adamforbes92/can2cluster/Images/WiFi3.jpg

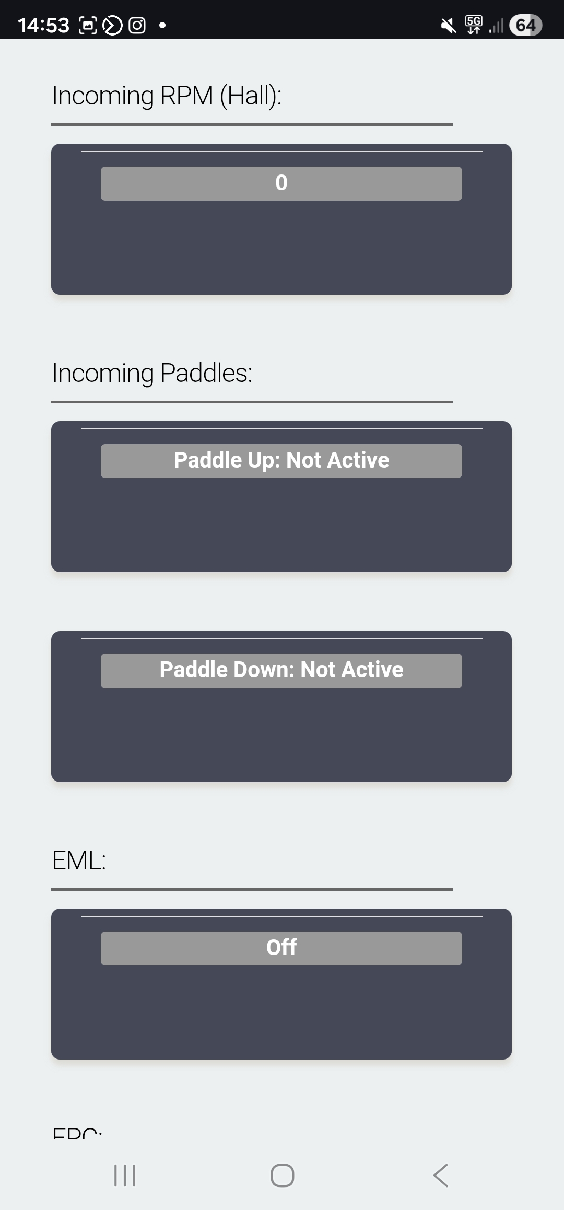
Images/WiFi3.jpg
