adamforbes92/can2cluster/Images/WiFi4.jpg

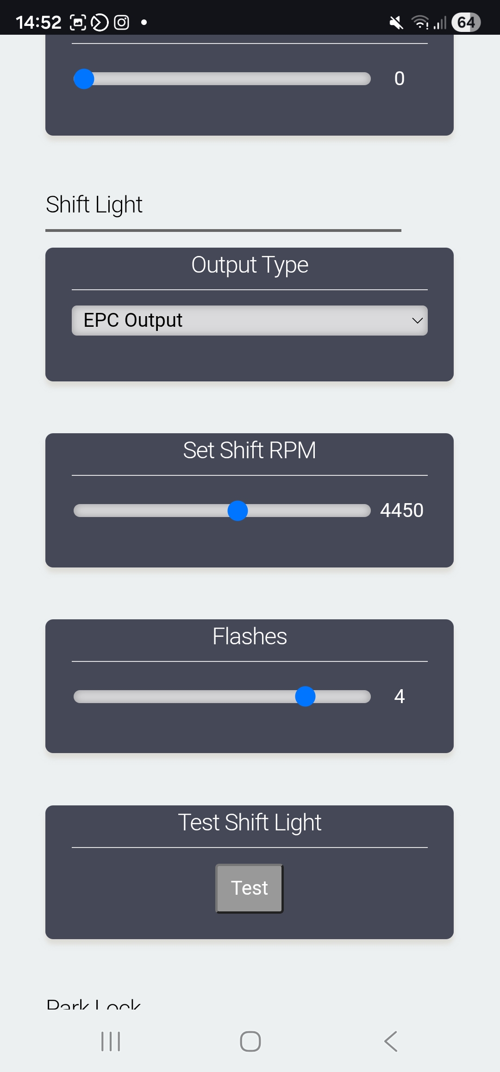
Images/WiFi4.jpg
