adamforbes92/can2cluster/Images/WiFi7.jpg

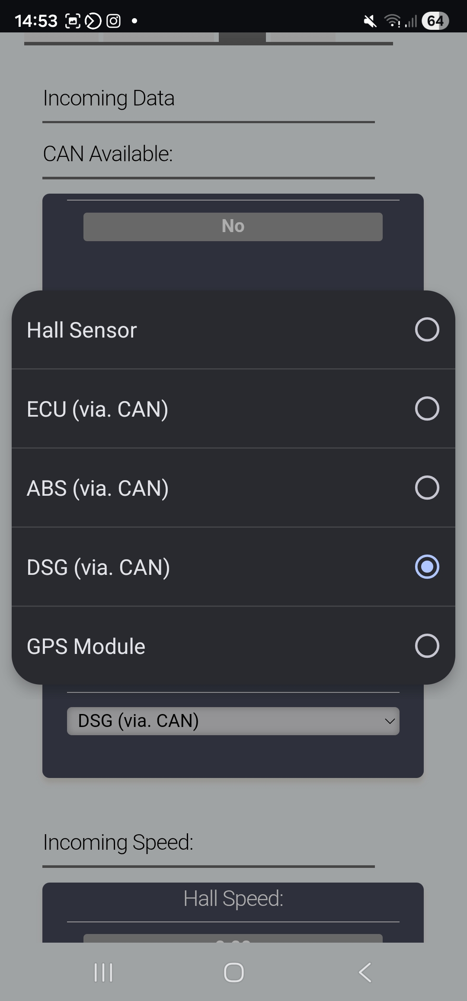
Images/WiFi7.jpg
