adamforbes92/can2cluster/PlatformIO/src/can2cluster_can.cpp

  #include "can2cluster_can.h"
#include "can2cluster_uds.h"
#include "can2cluster_savvycan.h"

void canInit()
{
  // Chassis CAN pins differ between boards (new board reuses GPIO16/26).
  const gpio_num_t txPin = (gpio_num_t)(isNewBoard ? pinTX_CAN_NEW : pinTX_CAN);
  const gpio_num_t rxPin = (gpio_num_t)(isNewBoard ? pinRX_CAN_NEW : pinRX_CAN);

  // Configure TWAI (CAN) controller
  twai_general_config_t g_config = TWAI_GENERAL_CONFIG_DEFAULT(txPin, rxPin, TWAI_MODE_NORMAL);
  g_config.rx_queue_len = 256;
  // Enable alerts so we can detect (and recover from) error-passive / bus-off events.
  g_config.alerts_enabled = TWAI_ALERT_BUS_OFF
                          | TWAI_ALERT_BUS_RECOVERED
                          | TWAI_ALERT_ERR_PASS
                          | TWAI_ALERT_ABOVE_ERR_WARN
                          | TWAI_ALERT_RX_QUEUE_FULL;
  twai_timing_config_t t_config = TWAI_TIMING_CONFIG_500KBITS();
  twai_filter_config_t f_config = TWAI_FILTER_CONFIG_ACCEPT_ALL();

  // Install TWAI driver
  if (twai_driver_install(&g_config, &t_config, &f_config) != ESP_OK)
  {
    DEBUG_CAN("TWAI driver install failed");
    return;
  }

  // Start TWAI driver
  if (twai_start() != ESP_OK)
  {
    DEBUG_CAN("TWAI start failed");
    return;
  }

  // Create a task to handle incoming CAN messages
  xTaskCreate(canReceiveTask, "canReceiveTask", 4096, NULL, 5, NULL);

  // Create a task to watch TWAI alerts and recover from bus-off
  xTaskCreate(canMonitorTask, "canMonitorTask", 3072, NULL, 4, NULL);
}

void canReceiveTask(void *args)
{
  twai_message_t rx_frame;
  while (1)
  {
    while (twai_receive(&rx_frame, 0) == ESP_OK)
    {
      onBodyRX(rx_frame);
      // Forward to SavvyCAN analyzer (no-op when analyzerMode and analyzerSerial are both false)
      analyzerQueueFrame(rx_frame, 0);
      // Route TP2.0 frames to the TP2.0 task queue
      if (tp20RxQueue &&
          (rx_frame.identifier == TP20_DSG_SETUP_RX ||
           rx_frame.identifier == TP20_RX_ID)) {
        xQueueSendToBack(tp20RxQueue, &rx_frame, 0);
      }
      // Route UDS response frames to the UDS task queue
      if (udsRxQueue && rx_frame.identifier == UDS_RX_ID) {
        xQueueSendToBack(udsRxQueue, &rx_frame, 0);
      }
    }
    vTaskDelay(1);
  }
}

// Monitors TWAI alerts and drives bus-off recovery.
//
// Sequence on bus-off:
//   1. TWAI_ALERT_BUS_OFF fires.
//   2. We call twai_initiate_recovery(), which puts the controller into
//      "recovering" state. The controller waits for 128 occurrences of
//      11 consecutive recessive bits before returning to "stopped".
//   3. TWAI_ALERT_BUS_RECOVERED fires when that completes.
//   4. We call twai_start() to bring the driver back online.
void canMonitorTask(void *args)
{
  while (1)
  {
    uint32_t alerts = 0;
    // Block up to 1 s waiting for an alert. read_alerts also clears the bits.
    if (twai_read_alerts(&alerts, pdMS_TO_TICKS(1000)) != ESP_OK)
    {
      continue;
    }

    if (alerts & TWAI_ALERT_ABOVE_ERR_WARN)
    {
      DEBUG_CAN("TWAI: error counter above warning level");
    }
    if (alerts & TWAI_ALERT_ERR_PASS)
    {
      DEBUG_CAN("TWAI: error-passive state entered");
    }
    if (alerts & TWAI_ALERT_RX_QUEUE_FULL)
    {
      DEBUG_CAN("TWAI: RX queue full — frames dropped");
    }
    if (alerts & TWAI_ALERT_BUS_OFF)
    {
      DEBUG_CAN("TWAI: BUS-OFF — initiating recovery");
      hasCAN = false;
      esp_err_t r = twai_initiate_recovery();
      if (r != ESP_OK)
      {
        DEBUG_CAN("TWAI: twai_initiate_recovery() returned %d", (int)r);
      }
    }
    if (alerts & TWAI_ALERT_BUS_RECOVERED)
    {
      DEBUG_CAN("TWAI: bus recovered — restarting driver");
      esp_err_t r = twai_start();
      if (r != ESP_OK)
      {
        DEBUG_CAN("TWAI: twai_start() after recovery returned %d", (int)r);
      }
    }
  }
}

void onBodyRX(const twai_message_t &frame)
{
#if ChassisCANDebug // print incoming CAN messages
  DEBUG_CHASSIS_CAN_("Length: %u ID: 0x%03X Buffer: ", frame.data_length_code, frame.identifier);
  for (uint8_t i = 0; i < frame.data_length_code; i++)
  {
    if (i > 0)
      Serial.print(" ");
    Serial.printf("%02X", frame.data[i]);
  }
  Serial.println();
#endif
  lastCAN = millis();
  hasCAN = true;

  switch (frame.identifier)
  {
  case MOTOR1_ID:
    // frame[2] (byte 3) > motor speed low byte
    // frame[3] (byte 4) > motor speed high byte
    // frame[4] (byte 3) > khm speed?
    vehicleRPMCAN = ((frame.data[3] << 8) | frame.data[2]) * 0.25; // conversion: 0.25*HEX
    break;

  case MOTOR2_ID:
    ecuSpeed = (frame.data[3] * 100 * 128) / 10000;
    break;

  case MOTOR3_ID:
    // Coolant temperature source. TODO(user): confirm the CAN ID, byte index
    // and scaling for your vehicle — this is a placeholder using the VW-style
    // "raw byte 0 minus 40 = degrees C" convention, mirroring how RPM is fixed.
    vehicleCoolantTemp = frame.data[0] - 40;
    break;

  case MOTOR5_ID:
    // set EML & EPC based on the bit read (LSB, so backwards)
    vehicleEML = bitRead(frame.data[1], 5);
    vehicleEPC = bitRead(frame.data[1], 6);
    break;

  case MOTOR6_ID:
    if (frame.data[0] == 0x73 || frame.data[0] == 0x72)
    {
      // vehicleReverse = true;
    }
    else
    {
      // vehicleReverse = false;
    }
    // Note: vehiclePark is authoritatively managed by gearLever_ID (0x448).
    // Only assert park from this frame; never clear it here to avoid racing.
    if (frame.data[0] == 0x83 || frame.data[0] == 0x82)
    {
      vehiclePark = true;
    }
    break;

  case BRAKES3_ID:
    if (1)
    {
      const uint16_t br3_speed_raw = (((uint16_t)frame.data[1] << 8) | frame.data[0]) >> 1;
      absSpeed = (uint16_t)(br3_speed_raw * 0.01f + 0.5f);
    }
    break;

  case mWaehlhebel_1_ID:
    gear_raw = ((frame.data[7] & 0b01110000) >> 4) - 1;
    lever_raw = (frame.data[7] & 0b00000001);

    if (lever_raw)
    {
      gear = gear_raw;
      switch (gear)
      {
      case 3:
        break;
      default:
        break;
      }

      if (gear == 0xFF)
      {
        gear = 1;
      }
    }
    break;

  case gearLever_ID:
    lever = (frame.data[0] & 0b11110000) >> 4;
    switch (lever)
    {
    case LEVER_P:
      vehiclePark = true;
      vehicleReverse = false;
      vehicleNeutral = false;
      break;
    case LEVER_R:
      vehiclePark = false;
      vehicleReverse = true;
      vehicleNeutral = false;
      break;
    case LEVER_N:
      vehiclePark = false;
      vehicleReverse = false;
      vehicleNeutral = true;
      break;
    case LEVER_D:
    case LEVER_S:
    case LEVER_TIPTRONIC_ON:
    case LEVER_TIPTRONIC_UP:
    case LEVER_TIPTRONIC_DOWN:
      vehiclePark = false;
      vehicleReverse = false;
      vehicleNeutral = false;
      break;
    }
    break;

  case emeraldECU1_ID:
    vehicleRPMCAN = ((frame.data[0] << 8) | frame.data[1]);
    break;

  case RENAULT_MEGANE_ECU:
    // Renault Megane engine RPM: bytes 0..1 big-endian, raw/8 (verified against
    // 2K/3K/4K/5K RPM logs — 4000 RPM reads 0x7D00).
    vehicleRPMCAN = (((uint16_t)frame.data[0] << 8) | frame.data[1]) >> 3;
    break;

  case emeraldECU2_ID:
    calcSpeed = ((frame.data[2] << 8) | frame.data[3]) * (2.25 / 256);
    break;

  case fordECU1_ID:
    vehicleRPMCAN = frame.data[1] & 0x00FF;
    vehicleRPMCAN |= (frame.data[0] << 8) & 0x7F00;
    break;

  case fordECU2_ID:
    vehicleOilPressure = (frame.data[5] >> 4) & 0x01;
    vehicleBattLight = (frame.data[4] >> 1) & 0x01;
    vehicleEML = (frame.data[4] >> 6) & 0x03;
    vehicleCoolantTemp = (frame.data[0] & 0xFF) - 40;
    break;

  case MOTOR_12:
  {
    // MQB Motor_12 (0x0A8) - SG_ MO_Drehzahl_01 : 48|16@1+ (0.25,0) [0|16383] "Unit_MinutInver"
    // i.e. engine speed (Drehzahl = revs) in RPM, factor 0.25/bit, 16-bit LE, bytes 6+7.
    const uint16_t mo_drehzahl_raw = ((uint16_t)frame.data[7] << 8) | frame.data[6];
    vehicleRPMCAN = (uint16_t)(mo_drehzahl_raw * 0.25f + 0.5f);
    break;
  }

  case MOTOR_07:
  {
    // MQB Motor_07 (0x640) - SG_ MO_Kuehlmitteltemp : 24|8@1+ (0.75,-48) "degC"  -> byte 3, coolant temperature
    const int16_t coolant_c = (int16_t)(frame.data[3] * 0.75f - 48.0f + 0.5f);
    vehicleCoolantTemp = (coolant_c > 0) ? (uint8_t)coolant_c : 0;
    break;
  }

  case MOTOR_18:
  {
    // MQB Motor_18 (0x670) - SG_ MO_EPCL : 13|3@1+  -> byte 1 bits 5..7, EPC lamp request (0 = off, >0 = lamp/text variants)
    // MQB has no engine MIL (EML) broadcast on FCAN - the check-engine
    // lamp is driven via the OBD/diagnostic path only, so vehicleEML has no MQB source.
    vehicleEPC = ((frame.data[1] >> 5) & 0x07) != 0;
    break;
  }

  case ESP_19:
  {
    // MQB ESP_19 (0x0B2) - per-wheel ABS speeds broadcast.
    // MQB FCAN K-matrix: four 16-bit LE wheel speeds (HL/HR/VL/VR) with
    // factor 0.0075 km/h per bit each.
    //   HL = Hinten Links  (rear left)   -> bytes 0..1
    //   HR = Hinten Rechts (rear right)  -> bytes 2..3
    //   VL = Vorne  Links  (front left)  -> bytes 4..5
    //   VR = Vorne  Rechts (front right) -> bytes 6..7
    // Average all four for a stable vehicle speed (ABS speed source).
    const uint16_t wheel_speed_hl_raw = (frame.data[1] << 8) | frame.data[0];
    const uint16_t wheel_speed_hr_raw = (frame.data[3] << 8) | frame.data[2];
    const uint16_t wheel_speed_vl_raw = (frame.data[5] << 8) | frame.data[4];
    const uint16_t wheel_speed_vr_raw = (frame.data[7] << 8) | frame.data[6];
    absSpeed = (wheel_speed_hl_raw + wheel_speed_hr_raw + wheel_speed_vl_raw + wheel_speed_vr_raw) * (0.0075 / 4.0);
    break;
  }

  case ESP_21:
  {
    // MQB ESP_21 (0x0FD) - ESP/ASR mode + reference speed.
    // MQB FCAN K-matrix:
    //   SG_ ESP_v_Signal : 16@1+ (0.01,0) "km/h"  -> bytes 4..5 LE, vehicle reference speed
    // Mapped to the ECU speed source so MQB works with either speed selection.
    ecuSpeed = (((uint16_t)frame.data[5] << 8) | frame.data[4]) * 0.01;
    break;
  }

  case GETRIEBE_11:
  {
    // MQB Getriebe_11 (0x0AD) - DSG status broadcast.
    //   SG_ GE_Fahrstufe : 42|4@1+  -> byte 5 bits 2..5, gear-lever position
    // Values: 0=init, 5=P, 6=R, 7=N, 8=D, 9=S, 13=tiptronic.
    //   SG_ GE_Zielgang  -> byte 7 high nibble, target/engaged gear (1..7, 0 = none)
    // Verified against OpenHaldex MQB log "gears all inc tip and sport.csv".
    // Also feeds the PQ 'lever'/'gear' globals so the DSG speed source works on MQB.
    const uint8_t fahrstufe = (frame.data[5] >> 2) & 0x0F;
    const uint8_t zielgang = (frame.data[7] >> 4) & 0x0F;
    switch (fahrstufe)
    {
    case MQB_FAHRSTUFE_P:
      vehiclePark = true;
      vehicleReverse = false;
      vehicleNeutral = false;
      lever = LEVER_P;
      gear = 0;
      break;
    case MQB_FAHRSTUFE_R:
      vehiclePark = false;
      vehicleReverse = true;
      vehicleNeutral = false;
      lever = LEVER_R;
      gear = 0;
      break;
    case MQB_FAHRSTUFE_N:
      vehiclePark = false;
      vehicleReverse = false;
      vehicleNeutral = true;
      lever = LEVER_N;
      gear = 0;
      break;
    case MQB_FAHRSTUFE_D:
    case MQB_FAHRSTUFE_S:
    case MQB_FAHRSTUFE_TIP:
      vehiclePark = false;
      vehicleReverse = false;
      vehicleNeutral = false;
      lever = (fahrstufe == MQB_FAHRSTUFE_D) ? LEVER_D
              : (fahrstufe == MQB_FAHRSTUFE_S) ? LEVER_S
                                               : LEVER_TIPTRONIC_ON;
      gear = (zielgang >= 1 && zielgang <= 6) ? zielgang : 0;
      break;
    default:
      // init / unknown - leave current state untouched
      break;
    }
    break;
  }

  case SHIFTER_PADDLE_ID:
  {
    // A real frame from the factory selector (we never receive our own TX).
    // Its presence switches broadcastGRA() into shadow mode.
    shifterRealSeenMs = millis();

    // Shadow: while a paddle press is being held, re-send this exact frame
    // straight away with only the state nibble swapped. Counter and the
    // handshake answer bytes (D3/D4) are the selector's own, so they stay
    // valid. Nothing is sent while idle. See SHIFTER_PADDLE_ID comment.
    const uint8_t txState = shifterTxState;
    if (txState != 0 && frame.data_length_code >= 4)
    {
      twai_message_t shadow = frame;
      shadow.data[1] = (txState << 4) | (frame.data[1] & 0x0F);
      shadow.data[0] = (~shadow.data[1] & 0xF0) | (frame.data[0] & 0x0F);
      if (twai_transmit(&shadow, pdMS_TO_TICKS(5)) != ESP_OK)
      { // failed, ignore - the next real frame is 10 ms away
      }
    }

#if serialDebugPaddles
    // Debug-only decode of the selector's own tip gate. Not wired into
    // padUpFunc/padDownFunc so it can't feed back into our own emulation.
    const uint8_t stateNibble = (frame.data[1] >> 4) & 0x0F;
    if (stateNibble == SHIFTER_PADDLE_STATE_UP)
    {
      DEBUG_PADDLES("Shifter CAN 0x%03X: paddle UP", SHIFTER_PADDLE_ID);
    }
    else if (stateNibble == SHIFTER_PADDLE_STATE_DOWN)
    {
      DEBUG_PADDLES("Shifter CAN 0x%03X: paddle DOWN", SHIFTER_PADDLE_ID);
    }
#endif
    break;
  }

  case SHIFTER_PADDLE_QUERY_ID:
  {
    // Gearbox -> shifter. Latch the payload so broadcastGRA() can answer the
    // query in its next 0x0AF frames (see SHIFTER_PADDLE_QUERY_ID comment).
    shifterQueryRaw = ((uint32_t)frame.data[0] << 16) | ((uint32_t)frame.data[1] << 8) | frame.data[2];
    shifterQueryMs = millis();

#if serialDebugPaddles
    // The hi-nibble is the paddle state the gearbox has accepted: the one
    // place that proves our 0x0AF frames are being taken seriously.
    static uint8_t lastAck = 0xFF;
    const uint8_t ack = frame.data[0] >> 4;
    if (ack != lastAck)
    {
      lastAck = ack;
      DEBUG_PADDLES("Gearbox CAN 0x%03X: accepted paddle state %s", SHIFTER_PADDLE_QUERY_ID,
                    (ack == 0xA) ? "UP" : (ack == 0xB) ? "DOWN" : (ack == 0xE) ? "idle" : "?");
    }
#endif
    break;
  }

  default:
    // do nothing...
    break;
  }

  // Aftermarket / Custom CAN speed input — parsed independently of the VW switch table
  if (useAftermarket && frame.identifier == (aftermarketSpeedID & 0x7FF)) {
    uint8_t lowIdx  = constrain(aftermarketSpeedLowByte,  0, 7);
    uint8_t highIdx = constrain(aftermarketSpeedHighByte, 0, 7);
    uint16_t rawValue;
    if (aftermarketSpeedLittleEndian) {
      // LSB at lowIdx, MSB at highIdx
      rawValue = (uint16_t)frame.data[lowIdx] | ((uint16_t)frame.data[highIdx] << 8);
    } else {
      // Big-endian: MSB at lowIdx, LSB at highIdx (mirrors broadcastSpeed convention)
      rawValue = (uint16_t)frame.data[highIdx] | ((uint16_t)frame.data[lowIdx] << 8);
    }
    double scaled = (rawValue * aftermarketSpeedScale) + aftermarketSpeedOffset;
    aftermarketSpeed = scaled < 0.0 ? 0.0 : scaled;
  }
}

void sendPaddleUpFrame()
{
  twai_message_t paddlesUp{}; // 0x7C0
  paddlesUp.identifier = GRA_ID;
  paddlesUp.data_length_code = 4;
  paddlesUp.data[0] = 0x0E;     // was 0xB7 chksum = byte 2 XOR byte 3 XOR byte 4
  paddlesUp.data[2] = 0x0C;     // was 0x34
  paddlesUp.data[3] = 0x02;     //
  bitSet(paddlesUp.data[3], 1); // set high (trigger)
  if (twai_transmit(&paddlesUp, pdMS_TO_TICKS(100)) != ESP_OK)
  {
    // failed, ignore
  }
}

void sendPaddleDownFrame()
{
  twai_message_t paddlesDown{}; // 0x7C0
  paddlesDown.identifier = GRA_ID;
  paddlesDown.data_length_code = 4;
  paddlesDown.data[0] = 0x0D; // chksum = byte 2 XOR byte 3 XOR byte
  paddlesDown.data[2] = 0x0C;
  paddlesDown.data[3] = 0x01;
  bitSet(paddlesDown.data[3], 1); // set high (trigger)
  if (twai_transmit(&paddlesDown, pdMS_TO_TICKS(100)) != ESP_OK)
  {
    // failed, ignore
  }
}

void broadcastGRA(void *args)
{
  // 0x01 = down, 0x02 = up, 0x03 = both (MQB_PADDLE_* values). One latch feeds
  // three outputs with their own hold times:
  //   PQ GRA 0x38A      20 ms frame, 80 ms pulse (PQ only knows single up/down)
  //   MQB paddle 0x3DD  100 ms frame, MQB_PADDLE_HOLD_MS
  //   selector 0x0AF    10 ms frame (shadow or standalone), SHIFTER_PADDLE_HOLD_MS
  // paddleOutput (web UI) picks which of them actually go on the bus.
  uint8_t activePaddleCmd = 0x00;
  uint32_t graHoldUntilMs = 0;
  uint32_t mqbHoldUntilMs = 0;
  uint32_t shifterHoldUntilMs = 0;

  // This task runs at the selector's 10 ms frame rate (broadcastGRARefresh);
  // the slower frames are divided down from it.
  uint8_t tick = 0; // 0..9, wraps every 100 ms

  while (1)
  {
#if detailedDebugStack
    stackbroadcastGRA = uxTaskGetStackHighWaterMark(NULL); // for capturing how much memory the task is using
#endif

    // Only stream the paddle frames when DSG is the active speed source.
    // The PQ frame must be broadcast continuously (rolling counter + CRC) for
    // the paddles to work, so it can't be gated on a pending paddle press alone
    // — a one-shot frame would break counter/checksum continuity. When DSG isn't
    // selected, nothing goes on the bus and any stale paddle triggers are cleared.
    if (!useDSG)
    {
      padUpTxPending = false;
      padDownTxPending = false;
      activePaddleCmd = 0x00;
      shifterTxState = 0;
      vTaskDelay(pdMS_TO_TICKS(broadcastGRARefresh));
      continue;
    }

    tick = (tick + 1) % 10;
    const bool tick20 = (tick % 2) == 0;
    const bool tick100 = tick == 0;

    const bool sendPQ = (paddleOutput == "PQ") || (paddleOutput == "All");
    const bool sendMQB = (paddleOutput == "MQB") || (paddleOutput == "All");
    const bool sendShifter = (paddleOutput == "Shifter") || (paddleOutput == "All");

    const uint8_t graPulseMS = 80; // PQ GRA: how long to hold the paddle signal high for (ms)

    // Latch a fresh paddle press into all three hold timers.
    uint8_t newCmd = 0x00;
    if (padUpTxPending && padDownTxPending)
    {
#if serialDebugPaddles
      DEBUG_PADDLES("Paddle up/down triggered together");
#endif
      newCmd = MQB_PADDLE_BOTH;
      padUpTxPending = false;
      padDownTxPending = false;
    }
    else if (padUpTxPending)
    {
#if serialDebugPaddles
      DEBUG_PADDLES("Paddle up");
#endif
      newCmd = MQB_PADDLE_UP;
      padUpTxPending = false;
    }
    else if (padDownTxPending)
    {
#if serialDebugPaddles
      DEBUG_PADDLES("Paddle down");
#endif
      newCmd = MQB_PADDLE_DOWN;
      padDownTxPending = false;
    }
    if (newCmd != 0x00)
    {
      const uint32_t now = millis();
      activePaddleCmd = newCmd;
      graHoldUntilMs = now + graPulseMS;
      mqbHoldUntilMs = now + MQB_PADDLE_HOLD_MS;
      shifterHoldUntilMs = now + SHIFTER_PADDLE_HOLD_MS;
    }

    uint8_t graCmd = 0x00;     // what the PQ GRA frame carries this tick
    uint8_t mqbCmd = 0x00;     // what the MQB 0x3DD frame carries this tick
    uint8_t shifterCmd = 0x00; // what the selector 0x0AF frame carries this tick
    if (activePaddleCmd != 0x00)
    {
      const uint32_t now = millis();
      if ((int32_t)(now - graHoldUntilMs) < 0)
      {
        graCmd = activePaddleCmd;
      }
      if ((int32_t)(now - mqbHoldUntilMs) < 0)
      {
        mqbCmd = activePaddleCmd;
      }
      if ((int32_t)(now - shifterHoldUntilMs) < 0)
      {
        shifterCmd = activePaddleCmd;
      }
      if (graCmd == 0x00 && mqbCmd == 0x00 && shifterCmd == 0x00)
      {
        activePaddleCmd = 0x00;
      }
    }

    // --- PQ GRA frame (emulated, 20 ms): rolling counter + XOR checksum. PQ
    // only recognises a single up/down, so a simultaneous press sends no pulse. ---
    if (sendPQ && tick20)
    {
      twai_message_t broadcastGRA{};
      broadcastGRA.identifier = GRA_ID;
      broadcastGRA.data_length_code = 4;
      broadcastGRA.data[1] = 0x00;        // always zero
      broadcastGRA.data[2] = GRA_counter; // full 8-bit rolling counter (0x00 > 0xFF)
      broadcastGRA.data[3] = (graCmd == MQB_PADDLE_BOTH) ? 0x00 : graCmd;

      GRA_crc = 0;
      for (uint8_t i = 2; i < 5; i++)
      {
        GRA_crc ^= broadcastGRA.data[i]; // xor byte 2, 3, 4
      }
      broadcastGRA.data[0] = GRA_crc;

      if (twai_transmit(&broadcastGRA, pdMS_TO_TICKS(100)) != ESP_OK)
      { // failed, ignore
      }

      GRA_counter++;
    }

    // --- MQB wheel-paddle frame (emulated, 100 ms): static carrier from a
    // customer's MQB capture, last byte is the paddle state. No counter/CRC.
    // See MQB_PADDLE_ID comment. ---
    if (sendMQB && tick100)
    {
      twai_message_t mqbPaddle{};
      mqbPaddle.identifier = MQB_PADDLE_ID;
      mqbPaddle.data_length_code = 8;
      mqbPaddle.data[0] = 0x08;
      mqbPaddle.data[1] = 0x04;
      mqbPaddle.data[2] = 0x20;
      mqbPaddle.data[3] = 0x00;
      mqbPaddle.data[4] = 0xFE;
      mqbPaddle.data[5] = 0x00;
      mqbPaddle.data[6] = 0x0A;
      mqbPaddle.data[7] = mqbCmd;

      if (twai_transmit(&mqbPaddle, pdMS_TO_TICKS(100)) != ESP_OK)
      { // failed, ignore
      }
    }

    // --- Selector paddle frame 0x0AF: real ID/encoding verified directly at
    // the selector module (see SHIFTER_PADDLE_ID comment). ---
    const uint8_t shifterState = (shifterCmd == MQB_PADDLE_UP)     ? SHIFTER_PADDLE_STATE_UP
                                 : (shifterCmd == MQB_PADDLE_DOWN) ? SHIFTER_PADDLE_STATE_DOWN
                                                                   : SHIFTER_PADDLE_STATE_IDLE;

    // Publish the held state for the shadow path in onBodyRX(); 0 keeps it quiet.
    shifterTxState = (!sendShifter || shifterState == SHIFTER_PADDLE_STATE_IDLE) ? 0 : shifterState;

    if (!sendShifter)
    {
      vTaskDelay(pdMS_TO_TICKS(broadcastGRARefresh));
      continue;
    }

    // Shadow mode: the factory selector is on the bus, so it owns 0x0AF.
    // onBodyRX() re-sends its frames with our state during a press; sending
    // our own free-running frame here would only collide with it.
    const uint32_t realSeenMs = shifterRealSeenMs;
    if (realSeenMs != 0 && (millis() - realSeenMs) < SHIFTER_PADDLE_REAL_TIMEOUT_MS)
    {
      vTaskDelay(pdMS_TO_TICKS(broadcastGRARefresh));
      continue;
    }

    // Standalone mode (no selector on the bus): send 0x0AF every 10 ms and
    // answer the gearbox's latest 0x128 query ourselves, exactly as the
    // factory selector does; with no recent query D3/D4 stay 00 00.
    uint8_t answerD3 = 0x00, answerD4 = 0x00;
    const uint32_t queryMs = shifterQueryMs;
    if (queryMs != 0 && (millis() - queryMs) < SHIFTER_PADDLE_QUERY_TIMEOUT_MS)
    {
      const uint32_t q = shifterQueryRaw;
      const uint8_t qD1 = (q >> 16) & 0xFF, qD2 = (q >> 8) & 0xFF, qD3 = q & 0xFF;
      if ((qD1 & 0x0F) == 0x5)
      {
        static const char ident[] = SHIFTER_PADDLE_IDENT;
        answerD4 = 0x01;
        if (qD2 != 0xFF)
        {
          answerD3 = (qD3 == 0xFF) ? (uint8_t)~qD2 : qD2; // complement / echo
        }
        else if (qD3 < sizeof(ident) - 1)
        {
          answerD3 = (uint8_t)ident[qD3]; // part number byte n
        }
        else
        {
          answerD3 = 0x00; // n >= 16 (up to 0x13) answers 0x00 on the real module
        }
      }
    }

    twai_message_t shifterPaddle{};
    shifterPaddle.identifier = SHIFTER_PADDLE_ID;
    shifterPaddle.data_length_code = 4;
    shifterPaddle.data[1] = (shifterState << 4) | (shifterPaddleCounter & 0x0F);
    shifterPaddle.data[0] = (~shifterPaddle.data[1] & 0xF0) | 0x02;
    shifterPaddle.data[2] = answerD3;
    shifterPaddle.data[3] = answerD4;

    if (twai_transmit(&shifterPaddle, pdMS_TO_TICKS(100)) != ESP_OK)
    { // failed, ignore
    }

    shifterPaddleCounter++;

    vTaskDelay(pdMS_TO_TICKS(broadcastGRARefresh));
  }
}

void broadcastSpeed(void *args)
{
  while (1)
  {
#if detailedDebugStack
    stackbroadcastSpeed = uxTaskGetStackHighWaterMark(NULL); // for capturing how much memory the task is using
#endif

    if (!broadcastSpeedEnabled)
    {
      vTaskDelay(pdMS_TO_TICKS(broadcastSpeedRefresh));
      continue;
    }

    twai_message_t speedFrame{};
    speedFrame.identifier = broadcastSpeedID & 0x7FF;
    speedFrame.extd = 0;
    speedFrame.data_length_code = constrain(broadcastSpeedDLC, 0, 8);

    for (uint8_t i = 0; i < 8; i++)
    {
      speedFrame.data[i] = broadcastSpeedData[i];
    }

    int32_t scaledSpeed = static_cast<int32_t>((vehicleSpeed * broadcastSpeedScale) + broadcastSpeedOffset);
    scaledSpeed = constrain(scaledSpeed, 0, 65535);
    broadcastSpeedValue = static_cast<uint16_t>(scaledSpeed);

    uint8_t lowByteIndex = constrain(broadcastSpeedLowByte, 0, 7);
    uint8_t highByteIndex = constrain(broadcastSpeedHighByte, 0, 7);
    uint8_t lowByte = static_cast<uint8_t>(broadcastSpeedValue & 0xFF);
    uint8_t highByte = static_cast<uint8_t>((broadcastSpeedValue >> 8) & 0xFF);

    if (broadcastSpeedLittleEndian)
    {
      speedFrame.data[lowByteIndex] = lowByte;
      speedFrame.data[highByteIndex] = highByte;
    }
    else
    {
      speedFrame.data[lowByteIndex] = highByte;
      speedFrame.data[highByteIndex] = lowByte;
    }

#if serialDebugIO
    DEBUG_IO_("TX SPEED ID:0x%03X DLC:%u Data:", speedFrame.identifier, speedFrame.data_length_code);
    for (uint8_t i = 0; i < speedFrame.data_length_code; i++)
    {
      DEBUG_IO_(" %02X", speedFrame.data[i]);
    }
    DEBUG_IO(" Value:%u (vehicleSpeed:%u)", broadcastSpeedValue, vehicleSpeed);
#endif

    if (twai_transmit(&speedFrame, pdMS_TO_TICKS(5)) != ESP_OK)
    {
      // frame dropped if TX queue is full
    }

    vTaskDelay(pdMS_TO_TICKS(broadcastSpeedRefresh));
  }
}
