adamforbes92/can2cluster/Code/can2cluster_wifi.ino

void setupUI() {
  ESPUI.setVerbosity(Verbosity::Quiet);  // turn off verbose debugging (Verbose for ON; Quiet for OFF)
  ESPUI.sliderContinuous = true;         // update slider valves constantly disabled.  No need and can cause crashes

  // create basic tab
  auto tabBasic = ESPUI.addControl(Tab, "", "Basic");
  ESPUI.addControl(Separator, "Needle Sweep", "", Dark, tabBasic);
  bool_NeedleSweep = ESPUI.addControl(Switcher, "Needle Sweep", String(hasNeedleSweep), Dark, tabBasic, generalCallback);
  int16_sweepSpeed = ESPUI.addControl(Slider, "Rate of Change (ms)", String(sweepSpeed), Dark, tabBasic, generalCallback);
  ESPUI.addControl(Min, "", "0", Dark, int16_sweepSpeed);
  ESPUI.addControl(Max, "", "50", Dark, int16_sweepSpeed);

  int16_stepRPM = ESPUI.addControl(Slider, "Rate RPM", String(stepRPM), Dark, tabBasic, generalCallback);
  ESPUI.addControl(Min, "", "100", Dark, int16_stepRPM);
  ESPUI.addControl(Max, "", "400", Dark, int16_stepRPM);

  int16_stepSpeed = ESPUI.addControl(Slider, "Rate Speed", String(stepSpeed), Dark, tabBasic, generalCallback);
  ESPUI.addControl(Min, "", "100", Dark, int16_stepSpeed);
  ESPUI.addControl(Max, "", "400", Dark, int16_stepSpeed);

  ESPUI.addControl(Button, "Test Needle Sweep", "Test", Dark, tabBasic, extendedCallback, (void *)11);

  // create advanced tab
  auto tabAdvanced = ESPUI.addControl(Tab, "", "Advanced Controls");
  ESPUI.addControl(Separator, "Testing", "", Dark, tabAdvanced);
  bool_testSpeedo = ESPUI.addControl(Switcher, "Test Speedo", "", Dark, tabAdvanced, generalCallback);
  int16_tempSpeed = ESPUI.addControl(Slider, "Go to Speed", String(tempSpeed), Dark, tabAdvanced, generalCallback);
  ESPUI.addControl(Min, "", "0", Dark, int16_tempSpeed);
  ESPUI.addControl(Max, "", "200", Dark, int16_tempSpeed);

  ESPUI.addControl(Separator, "RPM Output", "", Dark, tabAdvanced);
  bool_coilType = ESPUI.addControl(Switcher, "Coil Type", String(coilType), Dark, tabAdvanced, generalCallback);

  bool_testRPM = ESPUI.addControl(Switcher, "Test RPM", "", Dark, tabAdvanced, generalCallback);
  int16_tempRPM = ESPUI.addControl(Slider, "Go to RPM", String(tempRPM), Dark, tabAdvanced, generalCallback);
  ESPUI.addControl(Min, "", "0", Dark, int16_tempRPM);
  ESPUI.addControl(Max, "", "8000", Dark, int16_tempRPM);

  ESPUI.addControl(Separator, "Shift Light", "", Dark, tabAdvanced);
  int16_shiftLight = ESPUI.addControl(Select, "Output Type", "", Dark, tabAdvanced, generalCallback);
  ESPUI.addControl(Option, "None", "None", Dark, int16_shiftLight);
  ESPUI.addControl(Option, "EML Output", "EML", Dark, int16_shiftLight);
  ESPUI.addControl(Option, "EPC Output", "EPC", Dark, int16_shiftLight);
  ESPUI.addControl(Option, "EML & EPC Output", "Both", Dark, int16_shiftLight);

  int16_shiftRPM = ESPUI.addControl(Slider, "Set Shift RPM", String(shiftLimit), Dark, tabAdvanced, generalCallback);
  ESPUI.addControl(Min, "", "0", Dark, int16_shiftRPM);
  ESPUI.addControl(Max, "", "8000", Dark, int16_shiftRPM);

  int16_shiftFlashes = ESPUI.addControl(Slider, "Flashes", String(shiftFlashes), Dark, tabAdvanced, generalCallback);
  ESPUI.addControl(Min, "", "0", Dark, int16_shiftFlashes);
  ESPUI.addControl(Max, "", "5", Dark, int16_shiftFlashes);
  ESPUI.addControl(Button, "Test Shift Light", "Test", Dark, tabAdvanced, extendedCallback, (void *)12);

  ESPUI.addControl(Separator, "RPM Limits:", "", Dark, tabAdvanced);
  int16_maxRPM = ESPUI.addControl(Slider, "Maximum RPM", String(maxRPM), Dark, tabAdvanced, generalCallback);
  ESPUI.addControl(Min, "", "0", Dark, int16_minRPM);
  ESPUI.addControl(Max, "", "400", Dark, int16_maxRPM);
  ESPUI.addControl(Button, "Reset", "Reset", Dark, tabAdvanced, extendedCallback, (void *)13);

  ESPUI.addControl(Separator, "Speed Limits:", "", Dark, tabAdvanced);
  int16_maxSpeed = ESPUI.addControl(Slider, "Maximum Speed", String(maxSpeed), Dark, tabAdvanced, generalCallback);
  ESPUI.addControl(Min, "", "0", Dark, int16_minSpeed);
  ESPUI.addControl(Max, "", "400", Dark, int16_maxSpeed);
  ESPUI.addControl(Button, "Reset", "Reset", Dark, tabAdvanced, extendedCallback, (void *)14);

  ESPUI.addControl(Separator, "Hall Incoming Freq:", "", Dark, tabAdvanced);
  int16_maxHall = ESPUI.addControl(Slider, "Maximum Hall", String(maxFreqHall), Dark, tabAdvanced, generalCallback);
  ESPUI.addControl(Min, "", "0", Dark, int16_minHall);
  ESPUI.addControl(Max, "", "400", Dark, int16_maxHall);
  ESPUI.addControl(Button, "Reset", "Reset", Dark, tabAdvanced, extendedCallback, (void *)15);

  // create IO tab
  auto tabIO = ESPUI.addControl(Tab, "", "IO");
  ESPUI.addControl(Separator, "Incoming Data", "", Dark, tabIO);
  ESPUI.addControl(Separator, "CAN Available:", "", Dark, tabIO);
  label_hasCAN = ESPUI.addControl(Label, "", "0", Dark, tabIO, generalCallback);

  ESPUI.addControl(Separator, "GPS Available:", "", Dark, tabIO);
  label_hasGPS = ESPUI.addControl(Label, "", "Not Active", Dark, tabIO, generalCallback);

  ESPUI.addControl(Separator, "Speed Input:", "", Dark, tabIO);
  int16_speedType = ESPUI.addControl(Select, "Speed Type", "", Dark, tabIO, generalCallback);
  ESPUI.addControl(Option, "Hall Sensor", "Hall", Dark, int16_speedType);
  ESPUI.addControl(Option, "ECU (via. CAN)", "ECU", Dark, int16_speedType);
  ESPUI.addControl(Option, "ABS (via. CAN)", "ABS", Dark, int16_speedType);
  ESPUI.addControl(Option, "DSG (via. CAN)", "DSG", Dark, int16_speedType);
  ESPUI.addControl(Option, "GPS Module", "GPS", Dark, int16_speedType);

  ESPUI.addControl(Separator, "Incoming Speed:", "", Dark, tabIO);
  label_speedHall = ESPUI.addControl(Label, "Hall Speed:", "0", Dark, tabIO, generalCallback);
  label_speedECU = ESPUI.addControl(Label, "ECU Speed:", "0", Dark, tabIO, generalCallback);
  label_speedDSG = ESPUI.addControl(Label, "DSG Speed:", "0", Dark, tabIO, generalCallback);
  label_speedABS = ESPUI.addControl(Label, "ABS Speed:", "0", Dark, tabIO, generalCallback);
  label_speedGPS = ESPUI.addControl(Label, "GPS Speed:", "0", Dark, tabIO, generalCallback);

  ESPUI.addControl(Separator, "Incoming RPM (CAN):", "", Dark, tabIO);
  label_RPMCAN = ESPUI.addControl(Label, "", "0", Dark, tabIO, generalCallback);

  ESPUI.addControl(Separator, "Incoming Paddles:", "", Dark, tabIO);
  label_paddleUp = ESPUI.addControl(Label, "", "0", Dark, tabIO, generalCallback);
  label_paddleDown = ESPUI.addControl(Label, "", "0", Dark, tabIO, generalCallback);

  ESPUI.addControl(Separator, "Outputs:", "", Dark, tabIO);
  ESPUI.addControl(Separator, "Reverse:", "", Dark, tabIO);
  bool_testreverse = ESPUI.addControl(Switcher, "Test Reverse", "", Dark, tabIO, generalCallback);
  label_reverseActive = ESPUI.addControl(Label, "", "0", Dark, tabIO, generalCallback);

  ESPUI.addControl(Separator, "EML:", "", Dark, tabIO);
  bool_testeml = ESPUI.addControl(Switcher, "Test EML", "", Dark, tabIO, generalCallback);
  label_emlActive = ESPUI.addControl(Label, "", "0", Dark, tabIO, generalCallback);

  ESPUI.addControl(Separator, "EPC:", "", Dark, tabIO);
  bool_testepc = ESPUI.addControl(Switcher, "Test EPC", "", Dark, tabIO, generalCallback);
  label_epcActive = ESPUI.addControl(Label, "", "0", Dark, tabIO, generalCallback);

  //Finally, start up the UI.
  //This should only be called once we are connected to WiFi.
  ESPUI.begin(wifiHostName);
}

void updateCallback(Control *sender, int type) {
  updates = (sender->value.toInt() > 0);
}

void getTimeCallback(Control *sender, int type) {
  if (type == B_UP) {
    ESPUI.updateTime(mainTime);
  }
}

void graphAddCallback(Control *sender, int type) {
  if (type == B_UP) {
    ESPUI.addGraphPoint(graph, random(1, 50));
  }
}

void graphClearCallback(Control *sender, int type) {
  if (type == B_UP) {
    ESPUI.clearGraph(graph);
  }
}

void generalCallback(Control *sender, int type) {
#ifdef serialDebugWifi
  Serial.print("CB: id(");
  Serial.print(sender->id);
  Serial.print(") Type(");
  Serial.print(type);
  Serial.print(") '");
  Serial.print(sender->label);
  Serial.print("' = ");
  Serial.println(sender->value);
#endif

  uint8_t tempID = int(sender->id);
  switch (tempID) {
    case 3:
      hasNeedleSweep = sender->value.toInt();
      break;
    case 4:
      sweepSpeed = sender->value.toInt();
      break;
    case 7:
      stepRPM = sender->value.toInt();
      break;
    case 10:
      stepSpeed = sender->value.toInt();
      break;
      // 13 is needle sweep (in ext. portion below!)
    case 16:
      testSpeedo = sender->value.toInt();
      break;
    case 17:
      tempSpeed = sender->value.toInt();
      break;
    case 21:
      coilType = sender->value.toInt();
      break;
    case 22:
      testRPM = sender->value.toInt();
      break;
    case 23:
      tempRPM = sender->value.toInt();
      break;
    case 27:
      if (sender->value == "None") {
        useEMLShiftLight = false;
        useEPCShiftLight = false;
      }
      if (sender->value == "EML") {
        useEMLShiftLight = true;
        useEPCShiftLight = false;
      }
      if (sender->value == "EPC") {
        useEMLShiftLight = false;
        useEPCShiftLight = true;
      }
      if (sender->value == "Both") {
        useEMLShiftLight = true;
        useEPCShiftLight = true;
      }
    case 32:
      shiftLimit = sender->value.toInt();
      break;
    case 35:
      shiftFlashes = sender->value.toInt();
      break;
    case 40:
      maxRPM = sender->value.toInt();
      break;
    case 45:
      maxSpeed = sender->value.toInt();
      break;
    case 50:
      maxFreqHall = sender->value.toInt();
      break;

    case 61:
      if (sender->value == "Hall") {
        useHall = true;
        useECU = false;
        useDSG = false;
        useABS = false;
        useGPS = false;
      }
      if (sender->value == "ECU") {
        useHall = false;
        useECU = true;
        useDSG = false;
        useABS = false;
        useGPS = false;
      }
      if (sender->value == "DSG") {
        useHall = false;
        useECU = false;
        useDSG = true;
        useABS = false;
        useGPS = false;
      }
      if (sender->value == "ABS") {
        useHall = false;
        useECU = false;
        useDSG = false;
        useABS = true;
        useGPS = false;
      }
      if (sender->value == "GPS") {
        useHall = false;
        useECU = false;
        useDSG = false;
        useABS = false;
        useGPS = true;
      }
      break;

    case 80:
      testReverse = sender->value.toInt();
      break;
    case 83:
      testEML = sender->value.toInt();
      break;
    case 86:
      testEPC = sender->value.toInt();
      break;
  }
}

void extendedCallback(Control *sender, int type, void *param) {
#ifdef serialDebugWifi
  Serial.print("CB: id(");
  Serial.print(sender->id);
  Serial.print(") Type(");
  Serial.print(type);
  Serial.print(") '");
  Serial.print(sender->label);
  Serial.print("' = ");
  Serial.println(sender->value);
  Serial.print("param = ");
  Serial.println((long)param);
#endif

  uint8_t tempID = int(sender->id);
  switch (tempID) {
    case 13:
      if (type == B_UP) {
        tempNeedleSweep = true;
      }
      break;
    case 38:
      if (type == B_UP) {
        tempShiftLight = true;
      }
      break;
    case 43:
      if (type == B_UP) {
        maxRPM = 230;
        ESPUI.updateSlider(int16_maxRPM, maxRPM);
      }
      break;
    case 48:
      if (type == B_UP) {
        maxSpeed = 200;
        ESPUI.updateSlider(int16_maxSpeed, maxSpeed);
      }
      break;
    case 53:
      if (type == B_UP) {
        maxFreqHall = 200;
        ESPUI.updateSlider(int16_maxHall, maxFreqHall);
      }
      break;
  }
}

void selectCallback(Control *sender, int value) {
#ifdef serialDebugWifi
  Serial.print("Select: ID: ");
  Serial.print(sender->id);
  Serial.print(", Value: ");
  Serial.println(sender->value);
#endif
}

void connectWifi() {
  int connect_timeout;

  WiFi.hostname(wifiHostName);
  Serial.println("Begin wifi...");

  Serial.println("\nCreating access point...");
  WiFi.setTxPower(WIFI_POWER_8_5dBm);
  WiFi.mode(WIFI_AP);
  WiFi.softAPConfig(IPAddress(192, 168, 1, 1), IPAddress(192, 168, 1, 1), IPAddress(255, 255, 255, 0));
  WiFi.softAP(wifiHostName);
}

void textCallback(Control *sender, int type) {
  //This callback is needed to handle the changed values, even though it doesn't do anything itself.
}

void randomString(char *buf, int len) {
  for (auto i = 0; i < len - 1; i++)
    buf[i] = random(0, 26) + 'A';
  buf[len - 1] = '\0';
}

void disconnectWifi() {
  DEBUG("Number of connections: %d", WiFi.softAPgetStationNum());

  if (WiFi.softAPgetStationNum() == 0) {
    DEBUG("No connections, turning off");
    WiFi.disconnect(true, false);
    WiFi.mode(WIFI_OFF);
  }
}

void updateLabels(void *arg) {
  while (1) {
#if detailedDebugStack
    stackUpdateLabels = uxTaskGetStackHighWaterMark(NULL);  // for capturing how much memory the task is using
#endif

    if ((millis() + 10 - lastCAN) < 500) {
      hasCAN = true;
      hasError = false;
    } else {
      hasCAN = false;
      hasError = true;
    }

    if (useGPS) {
      if (gpsError) {
        ESPUI.updateLabel(label_hasGPS, String("Error: check connection!"));
      } else {
        if (hasGPS) {
          char bufhasGPS[50];
          sprintf(bufhasGPS, "Yes (%d satellites)", gps.satellites.value());
          ESPUI.updateLabel(label_hasGPS, String(bufhasGPS));
        } else {
          char bufhasGPS[50];
          sprintf(bufhasGPS, "No (%d satellites)", gps.satellites.value());
          ESPUI.updateLabel(label_hasGPS, String(bufhasGPS));
        }
      }
    }

    ESPUI.updateLabel(label_speedHall, String(hallSpeed));
    ESPUI.updateLabel(label_speedECU, String(ecuSpeed));
    ESPUI.updateLabel(label_speedGPS, String(gpsSpeed));
    ESPUI.updateLabel(label_speedDSG, String(dsgSpeed));
    ESPUI.updateLabel(label_speedABS, String(absSpeed));
    ESPUI.updateLabel(label_RPMCAN, String(vehicleRPM));

    hasCAN ? ESPUI.updateLabel(label_hasCAN, "Yes") : ESPUI.updateLabel(label_hasCAN, "No");

    !digitalRead(pinPaddleUp) || boolPadUp ? ESPUI.updateLabel(label_paddleUp, "Paddle Up: Active") : ESPUI.updateLabel(label_paddleUp, "Paddle Up: Not Active");
    !digitalRead(pinPaddleDown) || boolPadDown ? ESPUI.updateLabel(label_paddleDown, "Paddle Down: Active") : ESPUI.updateLabel(label_paddleDown, "Paddle Down: Not Active");
    vehicleReverse || testReverse ? ESPUI.updateLabel(label_reverseActive, "On") : ESPUI.updateLabel(label_reverseActive, "Off");
    vehicleEML || testEML ? ESPUI.updateLabel(label_emlActive, "On") : ESPUI.updateLabel(label_emlActive, "Off");
    vehicleEPC || testEPC ? ESPUI.updateLabel(label_epcActive, "On") : ESPUI.updateLabel(label_epcActive, "Off");

    if (useHall) {
      ESPUI.updateSelect(int16_speedType, "Hall");
    }
    if (useECU) {
      ESPUI.updateSelect(int16_speedType, "ECU");
    }
    if (useABS) {
      ESPUI.updateSelect(int16_speedType, "ABS");
    }
    if (useDSG) {
      ESPUI.updateSelect(int16_speedType, "DSG");
    }
    if (useGPS) {
      ESPUI.updateSelect(int16_speedType, "GPS");
    }

    if (!useEMLShiftLight && !useEPCShiftLight) {
      ESPUI.updateSelect(int16_shiftLight, "None");
    }
    if (useEMLShiftLight && !useEPCShiftLight) {
      ESPUI.updateSelect(int16_shiftLight, "EML");
    }
    if (!useEMLShiftLight && useEPCShiftLight) {
      ESPUI.updateSelect(int16_shiftLight, "EPC");
    }
    if (useEMLShiftLight && useEPCShiftLight) {
      ESPUI.updateSelect(int16_shiftLight, "Both");
    }
    vTaskDelay(labelRefresh / portTICK_PERIOD_MS);
  }
}
