adamforbes92/can2cluster/PlatformIO/src/can2cluster_dsg.cpp

#include "can2cluster_dsg.h"

// thanks to Drugward(!)

// Ratios, final drives and tire circumference are adjustable via the web UI
// (defaults in can2cluster_defs.cpp are DQ250 02E ratios).
double dq250_gear_ratio(uint8_t gear) {
  return (gear >= 1 && gear <= 6) ? dsgGearRatio[gear] : 1.0;
}

double dq250_final(uint8_t gear) {
  return (gear == 5 || gear == 6) ? dsgFinalDrive56 : dsgFinalDrive14;
}

double dq250_speed(uint16_t rpm_in, uint8_t gear) {
  double tireCircumference = dsgTireCirc;
  double rpm = (double)rpm_in * 1.0;
  double speed_mps = (rpm * tireCircumference) / (dq250_gear_ratio(gear) * dq250_final(gear) * 60);
  double vehicleSpeedTemp = speed_mps * 3.6;
  return vehicleSpeedTemp > 10 ? vehicleSpeedTemp : 1;  // ignore below 10km/h
}

void parseDSG(void *args) {
  static uint8_t lastGear = 0;
  static uint32_t gearSettleUntil = 0;
  static double dsgSpeedFiltered = 0;

  while (1) {
#if detailedDebugStack
    stackparseDSG = uxTaskGetStackHighWaterMark(NULL);  // for capturing how much memory the task is using
#endif

    if (vehicleRPM != 0 && gear != 0) {
      switch (lever) {
        case LEVER_D:
        case LEVER_S:
        case LEVER_TIPTRONIC_ON:
        case LEVER_TIPTRONIC_UP:
        case LEVER_TIPTRONIC_DOWN:
          // gear and vehicleRPM come from separate CAN frames; during a shift
          // they are transiently inconsistent (esp. MQB, where 'gear' is the
          // target gear and updates before RPM settles), which spikes the
          // calculated speed. Hold the last value briefly, then low-pass it.
          if (gear != lastGear) {
            lastGear = gear;
            gearSettleUntil = millis() + dsgGearSettleMs;
          }
          if (millis() >= gearSettleUntil) {
            double raw = dq250_speed(vehicleRPM, gear);
            dsgSpeedFiltered += (raw - dsgSpeedFiltered) * dsgSpeedSmoothing;
            dsgSpeed = dsgSpeedFiltered;
          }
          break;
        case LEVER_P:
          dsgSpeed = 0;
          dsgSpeedFiltered = 0;
        default:
          dsgSpeed = 0;
          dsgSpeedFiltered = 0;
          break;
      }
    } else if (gear == 0) {
      dsgSpeed = 0;  // no gear engaged (e.g. MQB P/R/N) - don't hold a stale value
      dsgSpeedFiltered = 0;
    }
    vTaskDelay(gearPause / portTICK_PERIOD_MS);
  }
}
