adamforbes92/can2cluster/Code/canbus2cluster_io.ino

void basicInit() {
// basic initialisation - setup pins for IO & setup CAN for receiving...
#if stateDebug
  Serial.begin(baudSerial);
  Serial.println(F("CAN-BUS to Cluster Initialising..."));
  Serial.println(F("Setting up pins..."));
#endif

  if (speedType == 2) {
    ss.begin(baudGPS);
#if stateDebug
    Serial.println(TinyGPSPlus::libraryVersion());
    Serial.println(F("Sats HDOP  Latitude   Longitude   Fix  Date       Time     Date Alt    Course Speed Card  Distance Course Card  Chars Sentences Checksum"));
    Serial.println(F("           (deg)      (deg)       Age                      Age  (m)    --- from GPS ----  ---- to London  ----  RX    RX        Fail"));
    Serial.println(F("----------------------------------------------------------------------------------------------------------------------------------------"));
#endif
  }
  setupPins();  // initialise the CAN chip
  setupButtons();

#if stateDebug
  Serial.println(F("Setup pins complete!"));
#endif

#if stateDebug
  Serial.println(F("CAN Chip Initialising..."));
#endif
  canInit();  // initialise the CAN chip
#if stateDebug
  Serial.println(F("CAN Chip Initialised!"));
#endif
}

void setupPins() {
  // define pin modes for outputs
  pinMode(onboardLED, OUTPUT);  // use the built-in LED for displaying errors!

  pinMode(pinSpeed, OUTPUT);
  pinMode(pinEML, OUTPUT);
  pinMode(pinEPC, OUTPUT);
  pinMode(pinReverse, OUTPUT);

#if hasCoilOutput
  pinMode(pinCoil, OUTPUT);
#endif
#if !hasCoilOutput
  pinMode(pinRPM, OUTPUT);
#endif

  // reset buttons if testLED is used (can be removed if 'testLED' is not used but keeping here for solidness)
  pinMode(pinPaddleUp, INPUT);
  pinMode(pinPaddleDown, INPUT);
  pinMode(pinSpare1, INPUT);
  pinMode(pinSpare2, INPUT);
}

void setupButtons() {
  //setup buttons / inputs
  btnPadUp.attachSingleClick(padUpFunc);      // call intSingle on a single click (single wipe)
  btnPadDown.attachSingleClick(padDownFunc);  // call intSingle on a single click (single wipe)

  btnSpare1.attachSingleClick(spare1Func);  // call intSingle on a single click (single wipe)
  btnSpare2.attachSingleClick(spare2Func);  // call intSingle on a single click (single wipe)
}

void needleSweep() {
  frequencyRPM = 0;
  frequencySpeed = 0;
  setFrequencyRPM(frequencyRPM);
  setFrequencySpeed(frequencySpeed);

  delay(needleSweepDelay);

#if stateDebug
  Serial.println(F("Starting needle sweep..."));
#endif

  // ramp up
  for (int i = 0; i < maxRPM; i++) {

    setFrequencySpeed(i * stepSpeed);
    setFrequencyRPM(i * stepRPM);
    delay(needleSweepDelay);
  }
  delay(needleSweepDelay);

  // ramp down
  for (int i = maxRPM; i > 0; i--) {  // set at >0 to stop the needle 'bouncing' when it returns to zero

    setFrequencySpeed(i * stepSpeed);
    setFrequencyRPM(i * stepRPM);
    delay(needleSweepDelay);
  }
  delay(needleSweepDelay);

  frequencyRPM = 0;
  frequencySpeed = 0;
  setFrequencyRPM(frequencyRPM);
  setFrequencySpeed(frequencySpeed);

  delay(needleSweepDelay);

#if stateDebug
  Serial.println(F("Finished needle sweep!"));
#endif
}

void blinkLED(int duration, int flashes, bool boolEPC, bool boolEML, bool boolRPM, bool boolSpeed) {
  for (int i = 0; i < flashes; i++) {
    if (boolEPC) {
      delay(duration);
      digitalWrite(pinEPC, HIGH);
      delay(duration);
      digitalWrite(pinEPC, LOW);
    }
    if (boolEML) {
      delay(duration);
      digitalWrite(pinEML, HIGH);
      delay(duration);
      digitalWrite(pinEML, LOW);
    }
    if (boolRPM) {
      delay(duration);
      digitalWrite(pinRPM, HIGH);
      delay(duration);
      digitalWrite(pinRPM, LOW);
    }
    if (boolSpeed) {
      delay(duration);
      digitalWrite(pinSpeed, HIGH);
      delay(duration);
      digitalWrite(pinSpeed, LOW);
    }
  }
}

void diagTest() {
  vehicleRPM = +1000;
  vehicleSpeed = +10;

  if (vehicleRPM > clusterRPMLimit) {
    vehicleRPM = 1000;
    frequencyRPM = 1;
  }
  if (vehicleSpeed > clusterSpeedLimit) {
    vehicleSpeed = 1;
    frequencySpeed = 1;
  }

  vehicleReverse = !vehicleReverse;
  digitalWrite(pinReverse, vehicleReverse);

  blinkLED(1000, 1, 1, 1, 0, 0);
}

void checkError() {
  if (hasError) {
    triggerLED = !triggerLED;
  } else {
    triggerLED = false;
  }

  if (triggerLED) {
    digitalWrite(onboardLED, HIGH);  // turn internal LED on
  } else {
    digitalWrite(onboardLED, LOW);  // turn internal LED off
  }
}
