adamforbes92/can2cluster/PlatformIO/include/can2cluster.h

#ifndef CAN2CLUSTER_H
#define CAN2CLUSTER_H

#include "can2cluster_defs.h"
#include "can2cluster_io.h"
#include "can2cluster_can.h"
#include "can2cluster_buttons.h"
#include "can2cluster_dsg.h"
#include "can2cluster_eep.h"
#include "can2cluster_gps.h"
#include "can2cluster_wifi.h"
#include "can2cluster_uds.h"
#include "can2cluster_savvycan.h"

#endif // CAN2CLUSTER_H
