adamforbes92/can2cluster/PlatformIO/include/can2cluster_buttons.h

#ifndef CAN2CLUSTER_BUTTONS_H
#define CAN2CLUSTER_BUTTONS_H

#include "can2cluster_defs.h"

void padUpFunc(void);
void padDownFunc(void);
void updateButtons(void);
void updatePaddleFeedback(void);

#endif // CAN2CLUSTER_BUTTONS_H
