adamforbes92/can2cluster/PlatformIO/include/can2cluster_wifi.h

#ifndef CAN2CLUSTER_WIFI_H
#define CAN2CLUSTER_WIFI_H

#include "can2cluster_defs.h"
#include <WiFi.h>
#include <ESPAsyncWebServer.h>

void setupUI(void);
void setupWebRoutes(void);

#endif // CAN2CLUSTER_WIFI_H
